JonChristensen/kelsus-manufacture/exports/k1/print/coupons/fit_ladder.stl

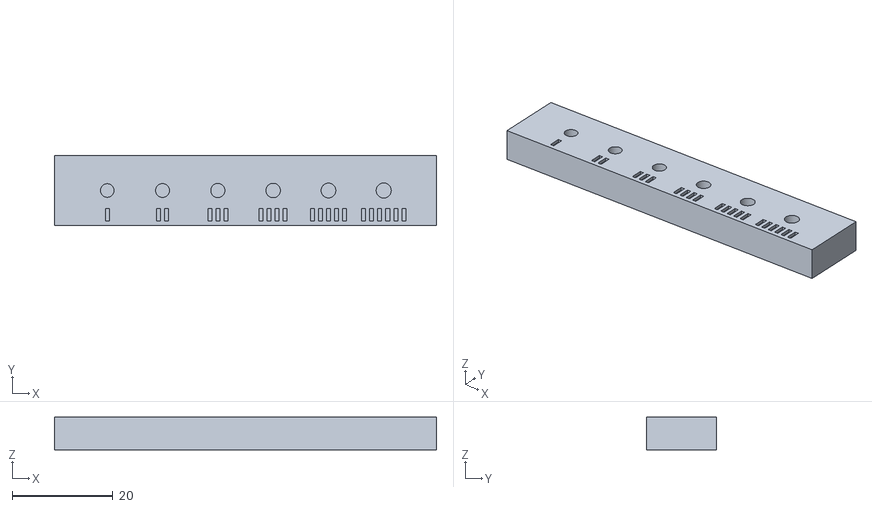
[picture p16: CAD file, 2026-10-07]
exports/k1/print/coupons/fit_ladder.stl
76.0 x 14.0 x 6.50
