JonChristensen/kelsus-manufacture/exports/k1/print/pallet_fork.stl

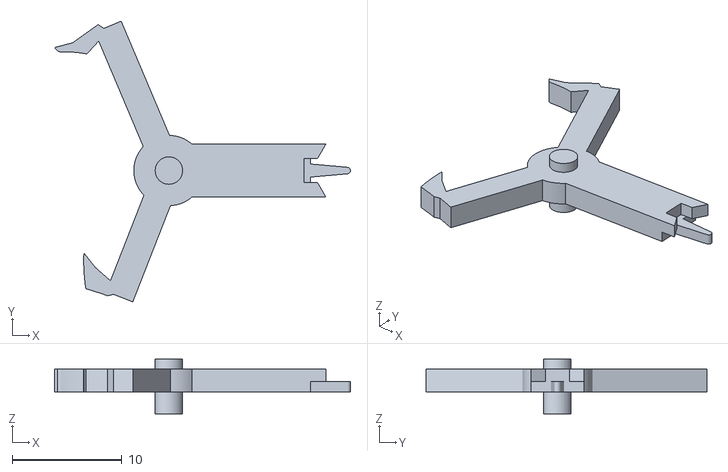
[picture p17: CAD file, 2026-10-07]
exports/k1/print/pallet_fork.stl
27.0 x 25.6 x 5.00
