JonChristensen/kelsus-manufacture/exports/k1/print/coupons/mesh_p6.stl

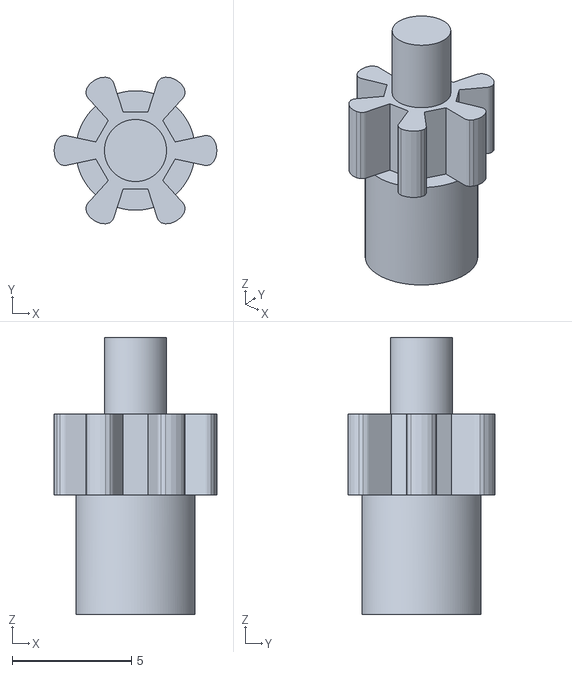
[picture p18: CAD file, 2026-10-07]
exports/k1/print/coupons/mesh_p6.stl
6.82 x 6.14 x 11.6
