JonChristensen/kelsus-manufacture/exports/k1/print/escape_wheel.stl

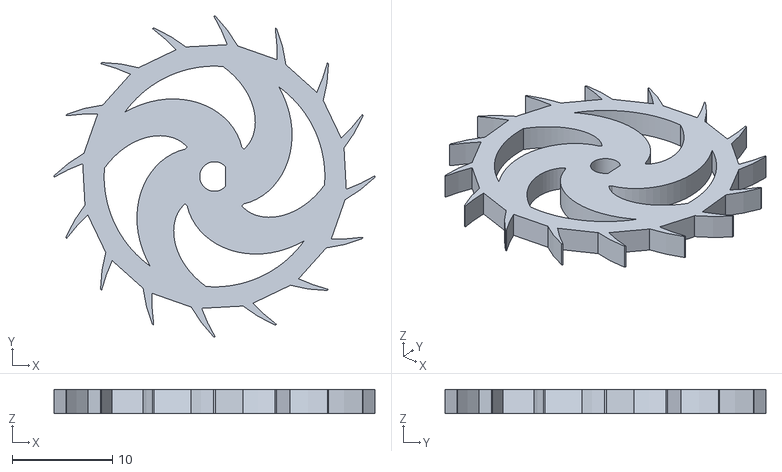
[picture p19: CAD file, 2026-10-07]
exports/k1/print/escape_wheel.stl
32.0 x 32.0 x 2.40
