JonChristensen/kelsus-manufacture/exports/k1/print/coupons/mesh_p7.stl

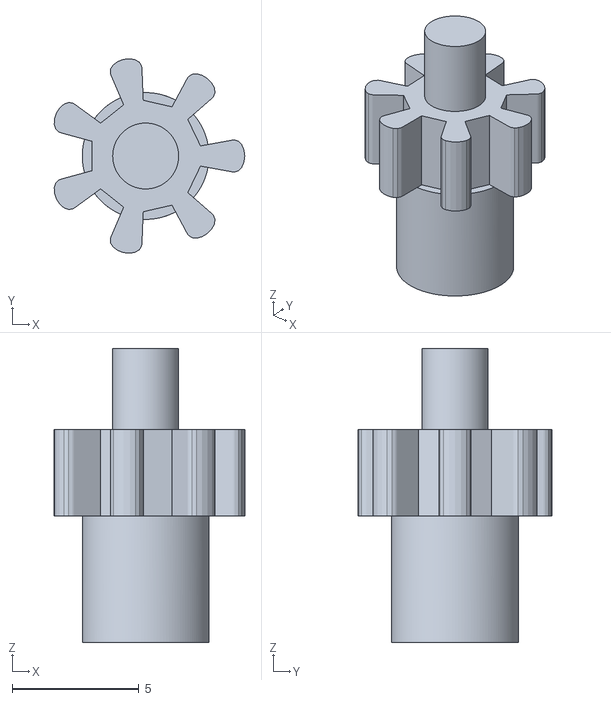
[picture p20: CAD file, 2026-10-07]
exports/k1/print/coupons/mesh_p7.stl
7.52 x 7.67 x 11.6
