JonChristensen/kelsus-manufacture/exports/k1/print/fourth_arbor.stl

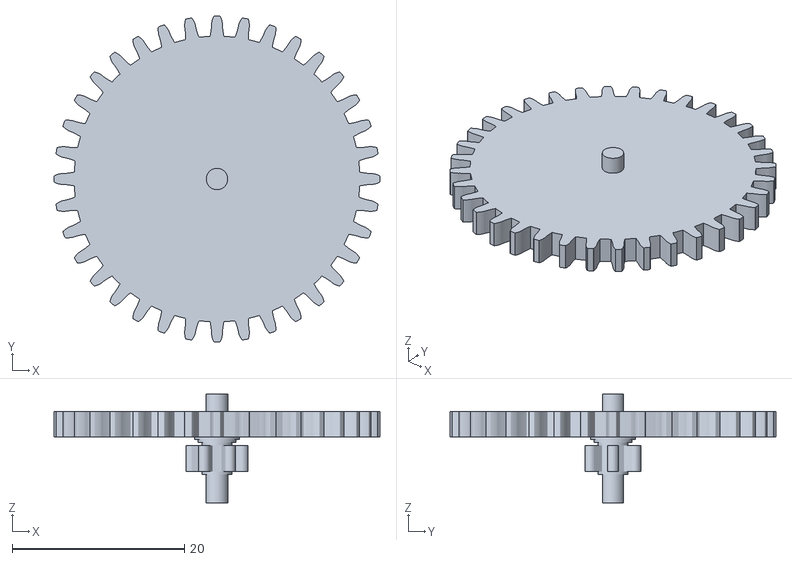
[picture p21: CAD file, 2026-10-07]
exports/k1/print/fourth_arbor.stl
37.9 x 37.9 x 12.7
