JonChristensen/kelsus-manufacture/exports/k1/print/coupons/mesh_w60.stl

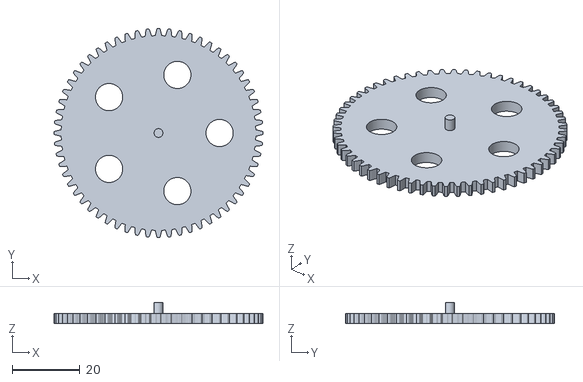
[picture p22: CAD file, 2026-10-07]
exports/k1/print/coupons/mesh_w60.stl
61.6 x 61.6 x 6.20
