JonChristensen/kelsus-manufacture/exports/k1/print/hairspring.stl

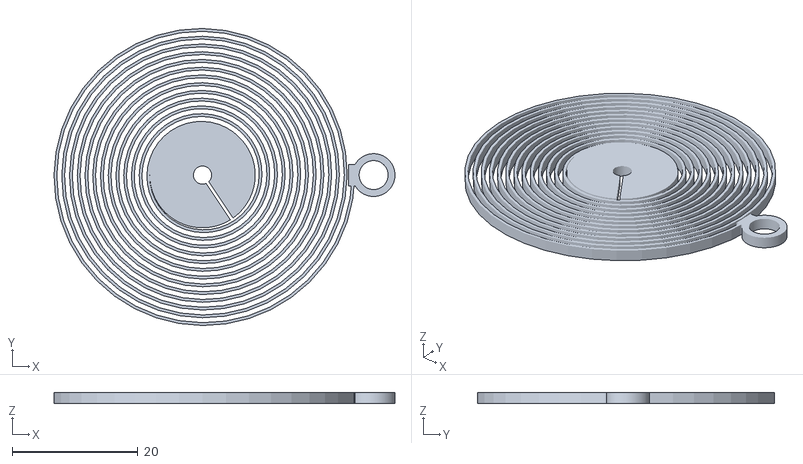
[picture p23: CAD file, 2026-10-07]
exports/k1/print/hairspring.stl
54.2 x 47.2 x 1.75
