JonChristensen/kelsus-manufacture/exports/k1/print/coupons/mesh_jig.stl

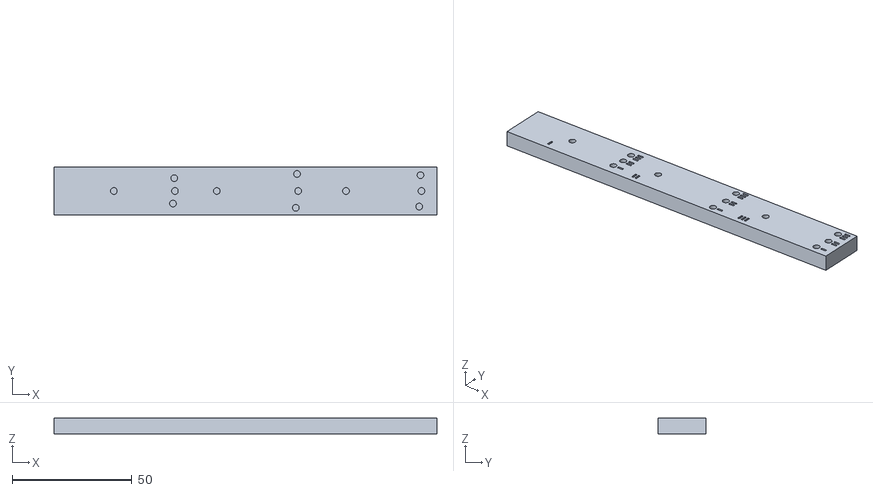
[picture p24: CAD file, 2026-10-07]
exports/k1/print/coupons/mesh_jig.stl
160.0 x 20.0 x 6.50
