JonChristensen/kelsus-manufacture/exports/k1/print/moon_disc.stl

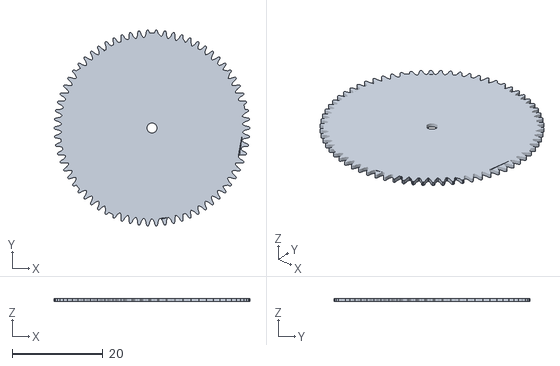
[picture p25: CAD file, 2026-10-07]
exports/k1/print/moon_disc.stl
43.3 x 43.2 x 0.75
