JonChristensen/kelsus-manufacture/exports/k1/print/transfer_idler.stl

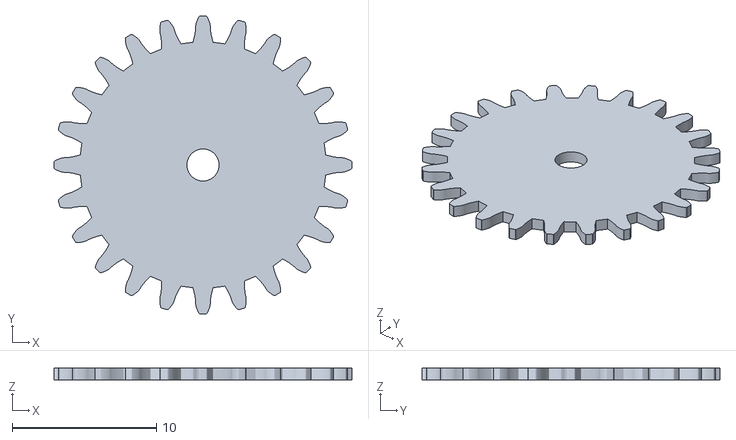
[picture p26: CAD file, 2026-10-07]
exports/k1/print/transfer_idler.stl
20.7 x 20.7 x 0.8
