JonChristensen/kelsus-manufacture/exports/k1/print/bay_strap.stl

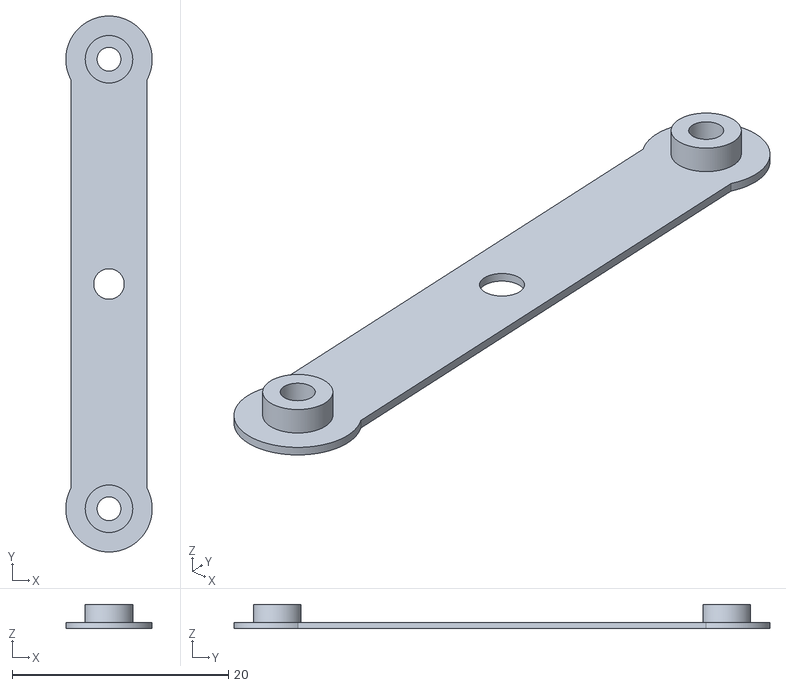
[picture p27: CAD file, 2026-10-07]
exports/k1/print/bay_strap.stl
8.00 x 49.6 x 2.25
