JonChristensen/kelsus-manufacture/exports/k1/print/balance_wheel.stl

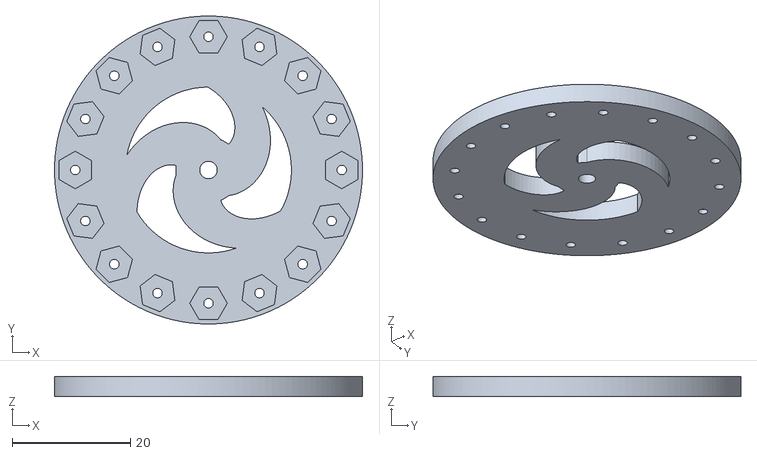
[picture p28: CAD file, 2026-10-07]
exports/k1/print/balance_wheel.stl
52.0 x 52.0 x 3.40
