JonChristensen/kelsus-manufacture/exports/k1/print/escape_arbor.stl

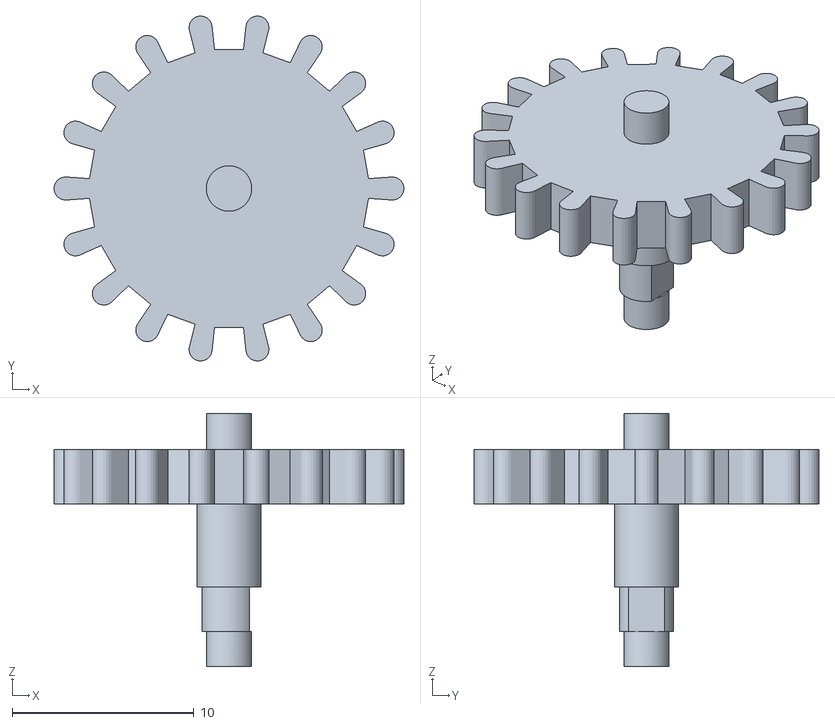
[picture p29: CAD file, 2026-10-07]
exports/k1/print/escape_arbor.stl
19.3 x 19.0 x 14.0
