JonChristensen/kelsus-manufacture/exports/k1/print/crown_stud.stl

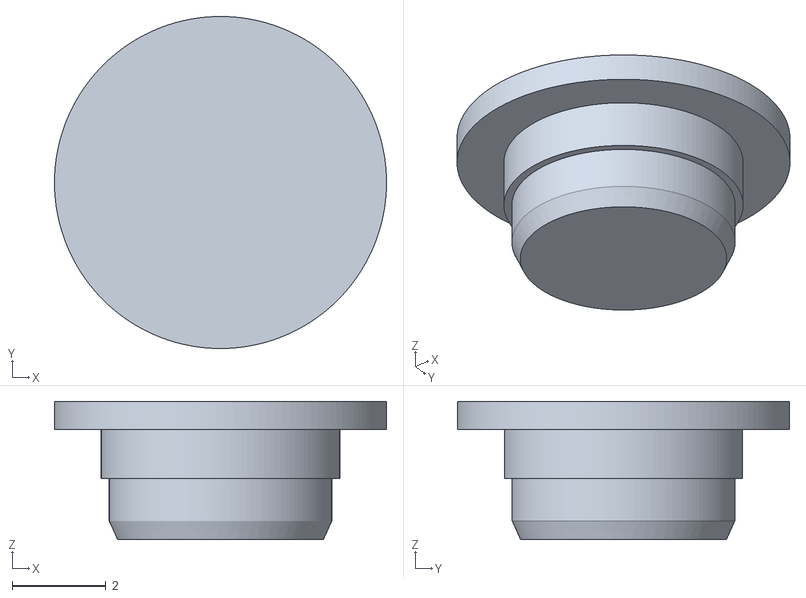
[picture p30: CAD file, 2026-10-07]
exports/k1/print/crown_stud.stl
7.10 x 7.10 x 2.96
