JonChristensen/kelsus-manufacture/exports/k1/print/moon_w2.stl

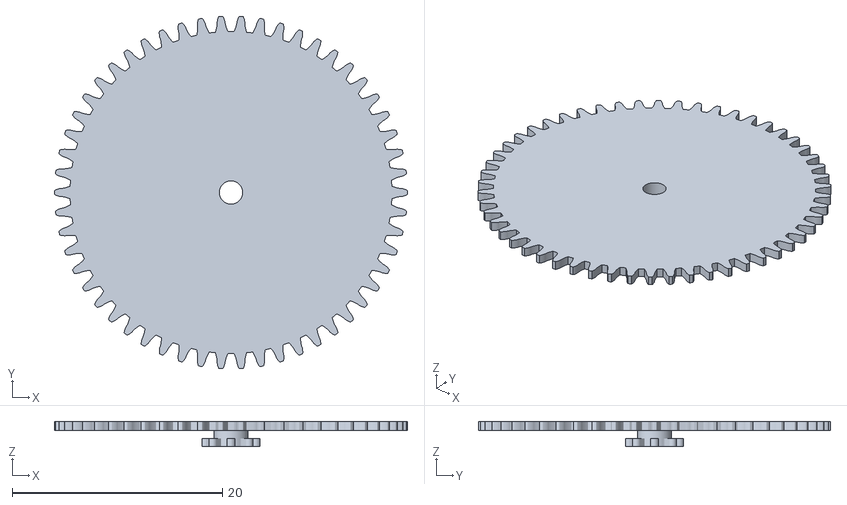
[picture p31: CAD file, 2026-10-07]
exports/k1/print/moon_w2.stl
33.6 x 33.6 x 2.40
