JonChristensen/kelsus-manufacture/exports/k1/print/hour_wheel.stl

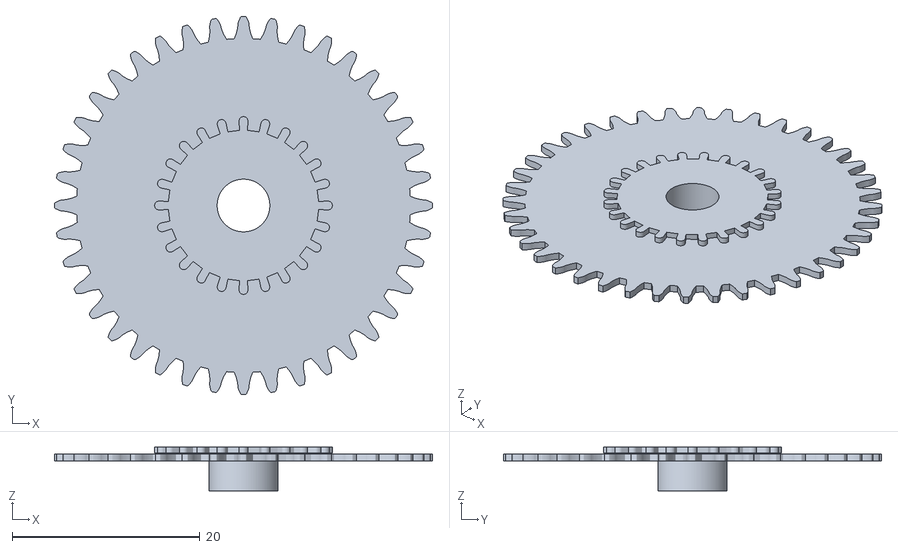
[picture p32: CAD file, 2026-10-07]
exports/k1/print/hour_wheel.stl
40.3 x 40.3 x 4.65
