JonChristensen/kelsus-manufacture/exports/k1/print/third_arbor.stl

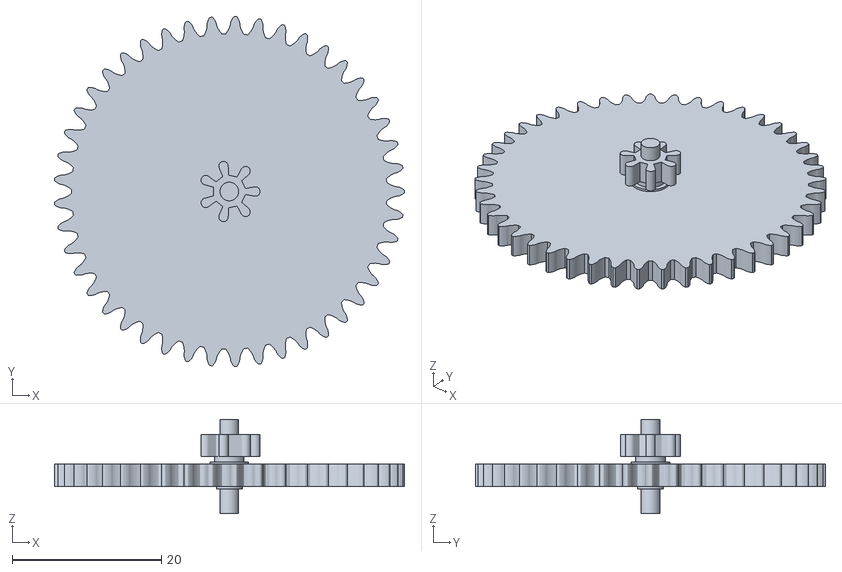
[picture p33: CAD file, 2026-10-07]
exports/k1/print/third_arbor.stl
46.9 x 47.0 x 12.7
