JonChristensen/kelsus-manufacture/exports/k1/print/balance_cock.stl

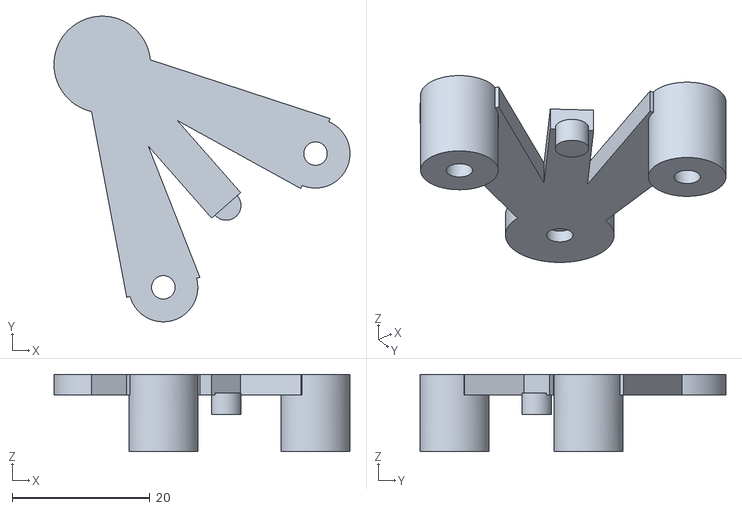
[picture p34: CAD file, 2026-10-07]
exports/k1/print/balance_cock.stl
42.9 x 44.3 x 11.2
