JonChristensen/kelsus-manufacture/exports/k1/print/moon_w1.stl

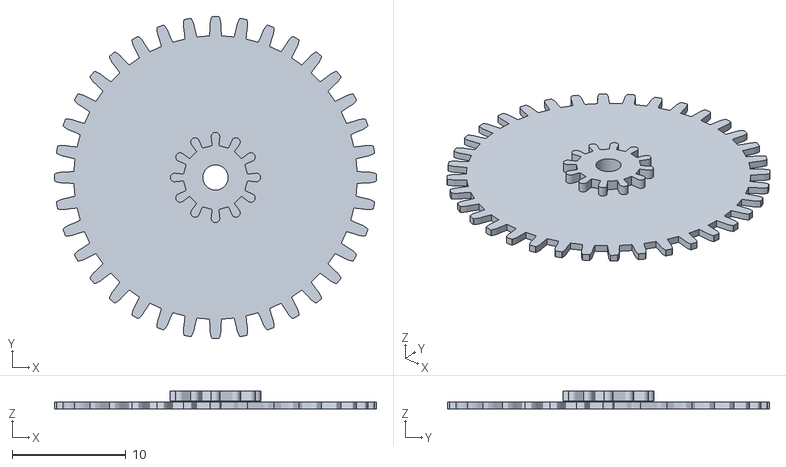
[picture p35: CAD file, 2026-10-07]
exports/k1/print/moon_w1.stl
28.3 x 28.3 x 1.55
