JonChristensen/kelsus-manufacture/exports/k1/print/roller.stl

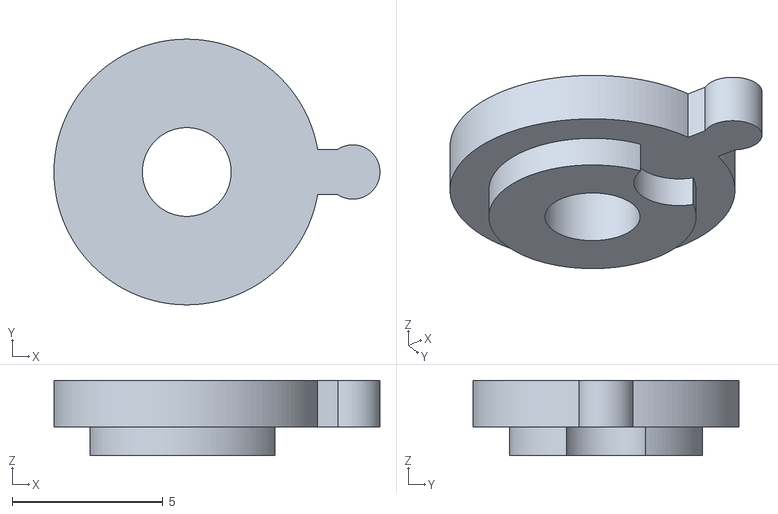
[picture p36: CAD file, 2026-10-07]
exports/k1/print/roller.stl
10.8 x 8.80 x 2.50
