JonChristensen/kelsus-manufacture/exports/k1/print/crown_wheel.stl

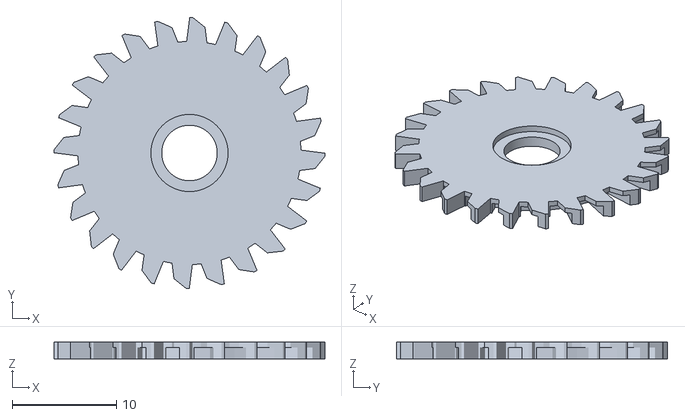
[picture p37: CAD file, 2026-10-07]
exports/k1/print/crown_wheel.stl
26.0 x 26.0 x 1.60
