JonChristensen/kelsus-manufacture/exports/k1/print/winding_pinion.stl

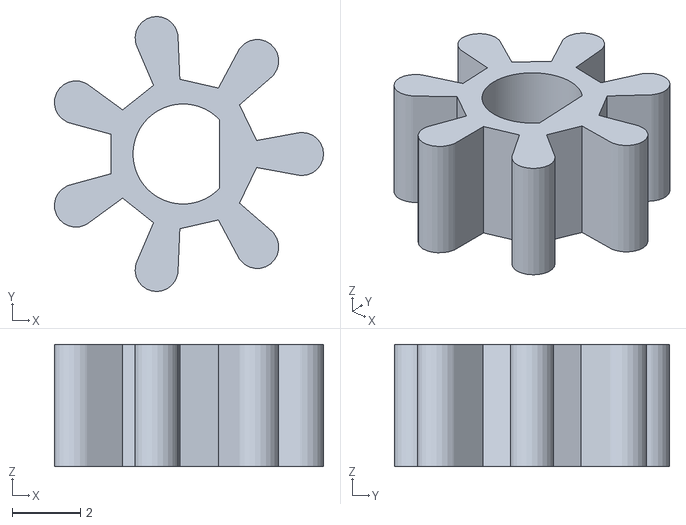
[picture p38: CAD file, 2026-10-07]
exports/k1/print/winding_pinion.stl
7.92 x 8.09 x 3.60
