JonChristensen/kelsus-manufacture/exports/k1/print/dial_sheet.stl

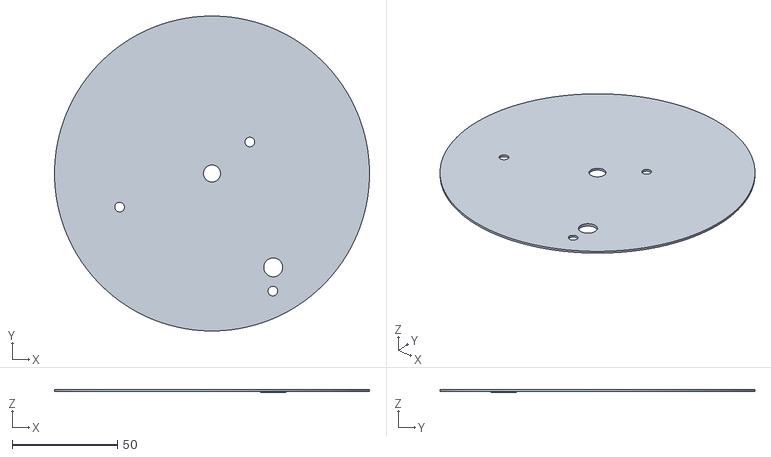
[picture p39: CAD file, 2026-10-07]
exports/k1/print/dial_sheet.stl
150.0 x 150.0 x 1.30
