JonChristensen/kelsus-manufacture/exports/k1/print/barrel_arbor.stl

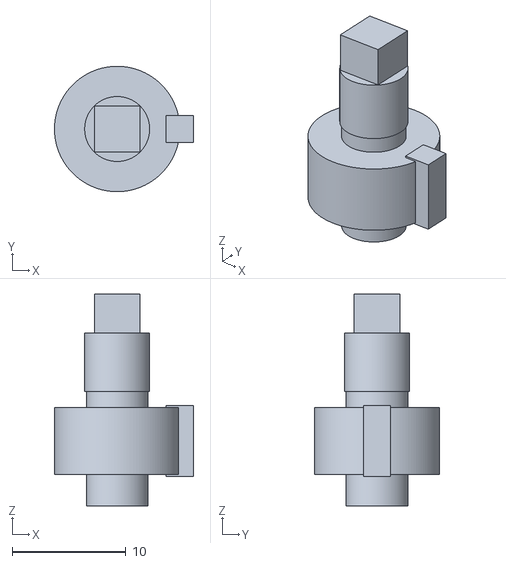
[picture p40: CAD file, 2026-10-07]
exports/k1/print/barrel_arbor.stl
12.2 x 11.0 x 18.6
