JonChristensen/kelsus-manufacture/exports/k1/print/minute_arbor.stl

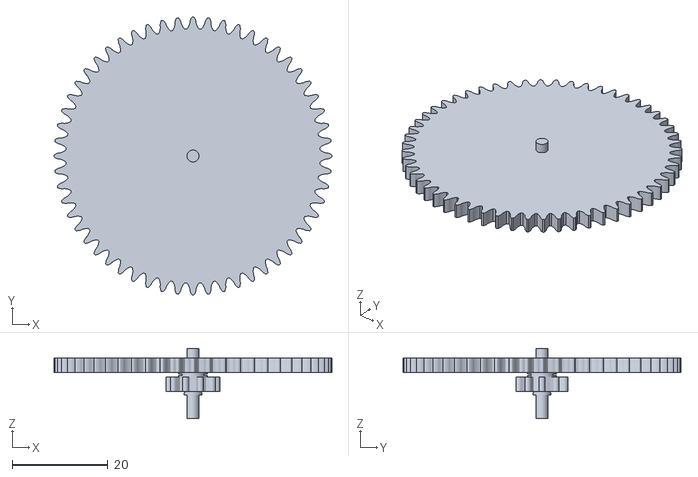
[picture p41: CAD file, 2026-10-07]
exports/k1/print/minute_arbor.stl
58.1 x 58.1 x 14.6
