JonChristensen/kelsus-manufacture/exports/k1/print/cannon.stl

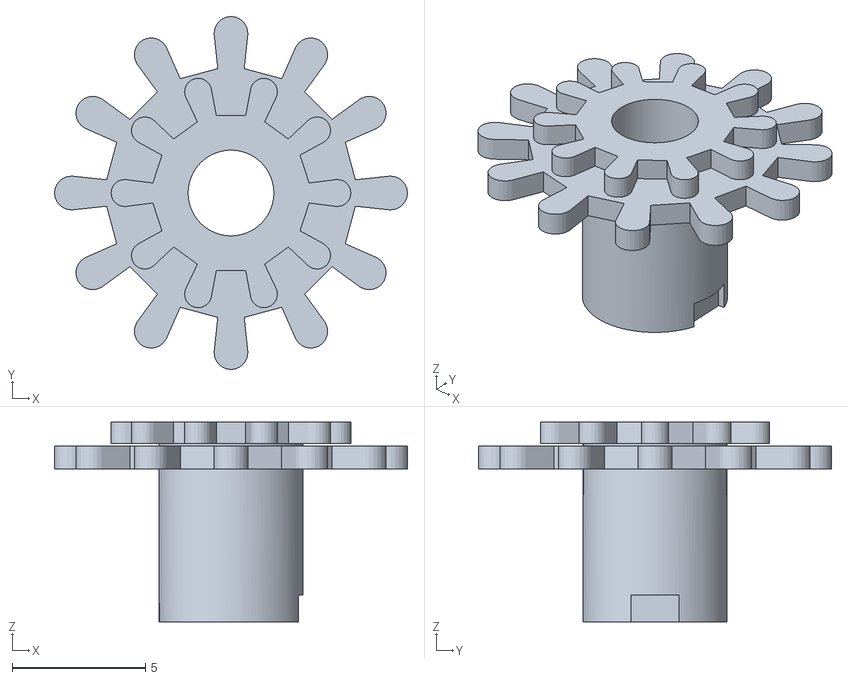
[picture p42: CAD file, 2026-10-07]
exports/k1/print/cannon.stl
13.3 x 13.3 x 7.50
