JonChristensen/kelsus-manufacture/exports/k1/print/stem_and_crown.stl

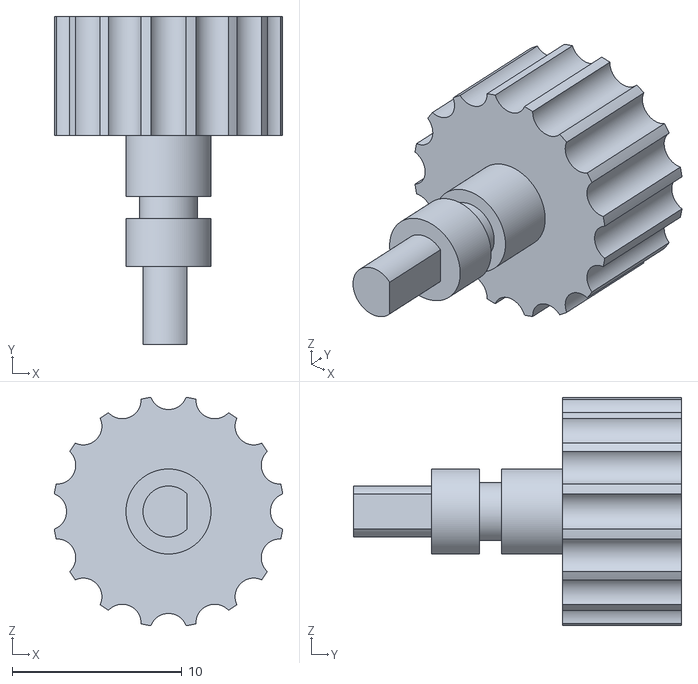
[picture p43: CAD file, 2026-10-07]
exports/k1/print/stem_and_crown.stl
13.4 x 19.3 x 13.4
