JonChristensen/kelsus-manufacture/exports/k1/print/drum.stl

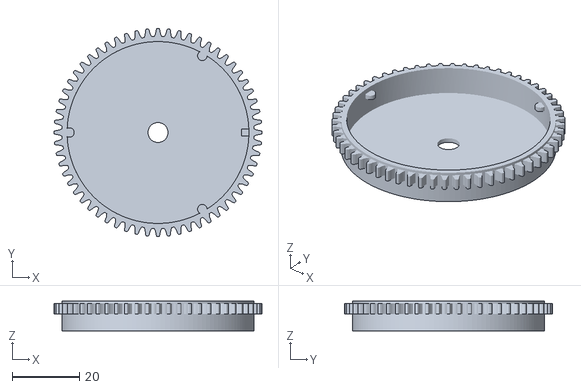
[picture p44: CAD file, 2026-10-07]
exports/k1/print/drum.stl
61.8 x 61.8 x 8.80
