JonChristensen/kelsus-manufacture/exports/k1/print/drum_cover.stl

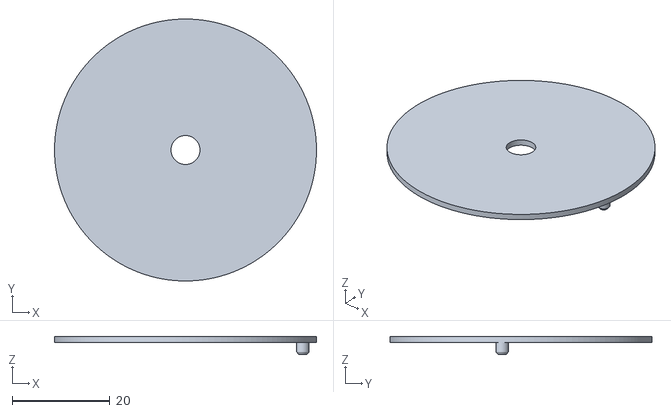
[picture p45: CAD file, 2026-10-07]
exports/k1/print/drum_cover.stl
53.6 x 53.6 x 3.70
