JonChristensen/kelsus-manufacture/exports/k1/print/ratchet.stl

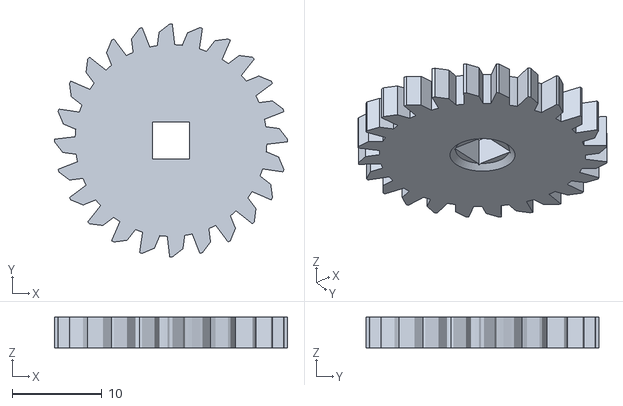
[picture p46: CAD file, 2026-10-07]
exports/k1/print/ratchet.stl
26.0 x 26.0 x 3.45
